Alexei-Orlov/2526_Maker_Fusor/Documentation/Spécificités pompe à vide.jpg

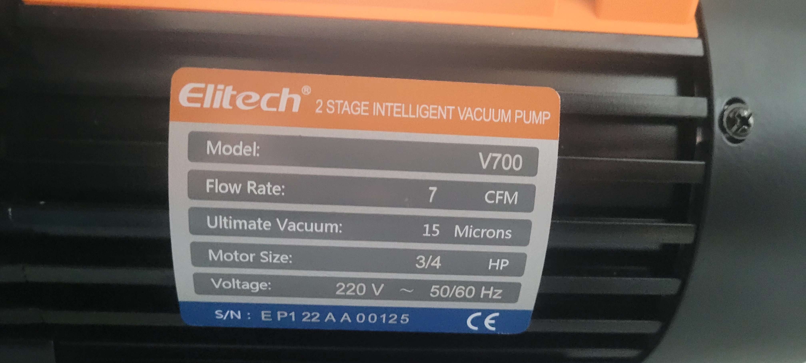
Documentation/Spécificités pompe à vide.jpg
