Alexei-Orlov/2526_Maker_Fusor/Documentation/Spécificités transformateur.jpg

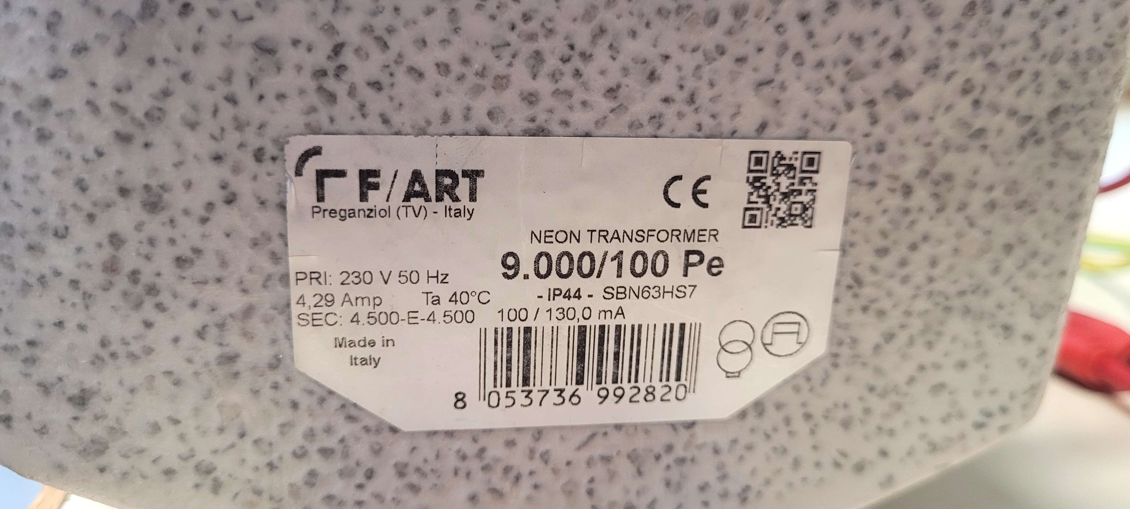
Documentation/Spécificités transformateur.jpg
