Alexei-Orlov/2526_Maker_Fusor/Documentation/Spécificités variac.jpg

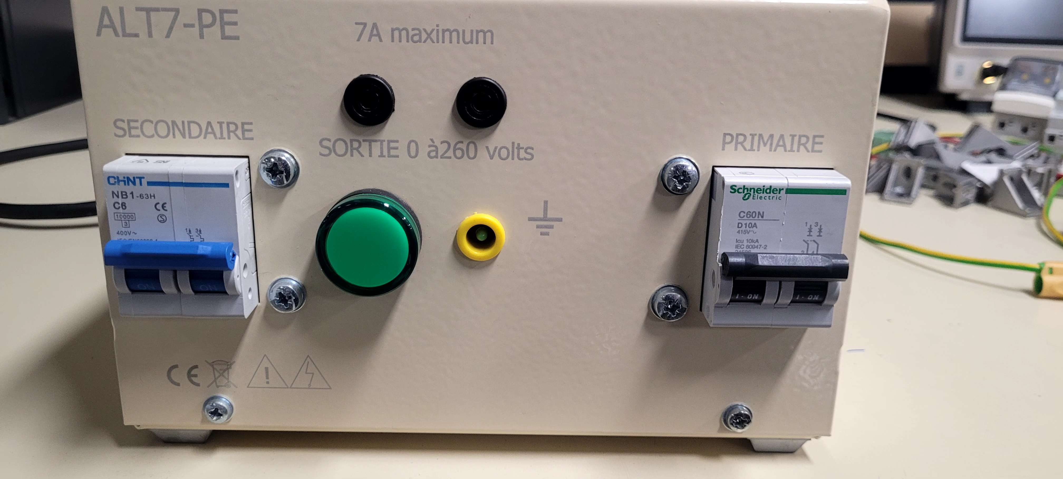
Documentation/Spécificités variac.jpg
